madsrumlenordstrom/Guitarpedal/pictures/IMG_1526.jpeg

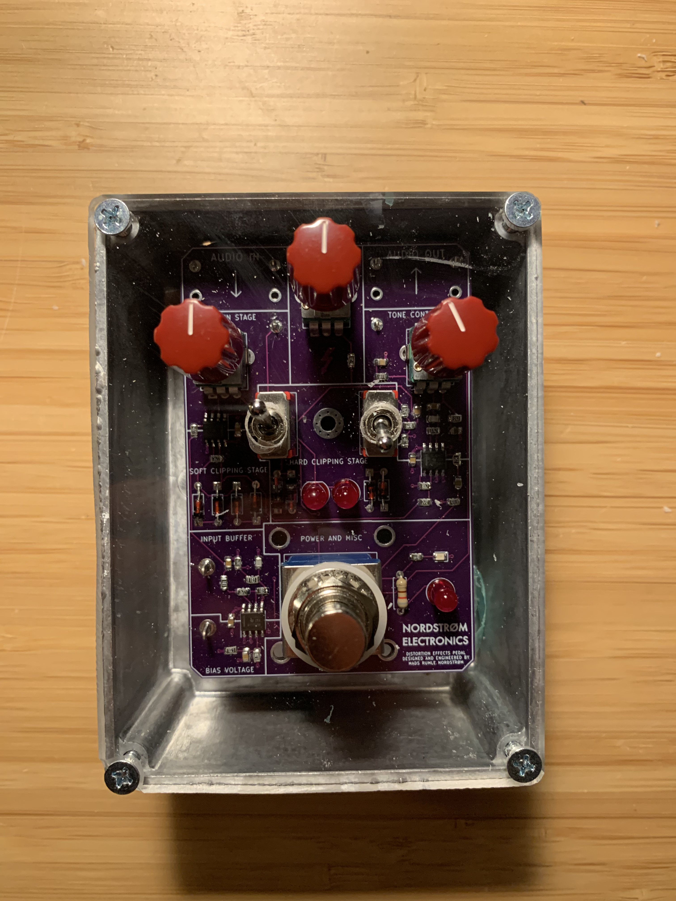
pictures/IMG_1526.jpeg
