madsrumlenordstrom/Guitarpedal/pictures/IMG_1527.jpeg

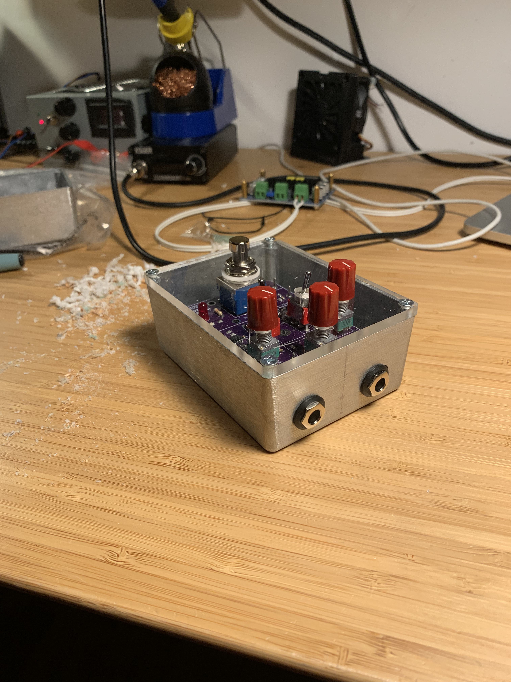
pictures/IMG_1527.jpeg
